LEDs-by-glowingkitty/GlowHub/GlowHubPCB/GlowHubPCBfiles.png

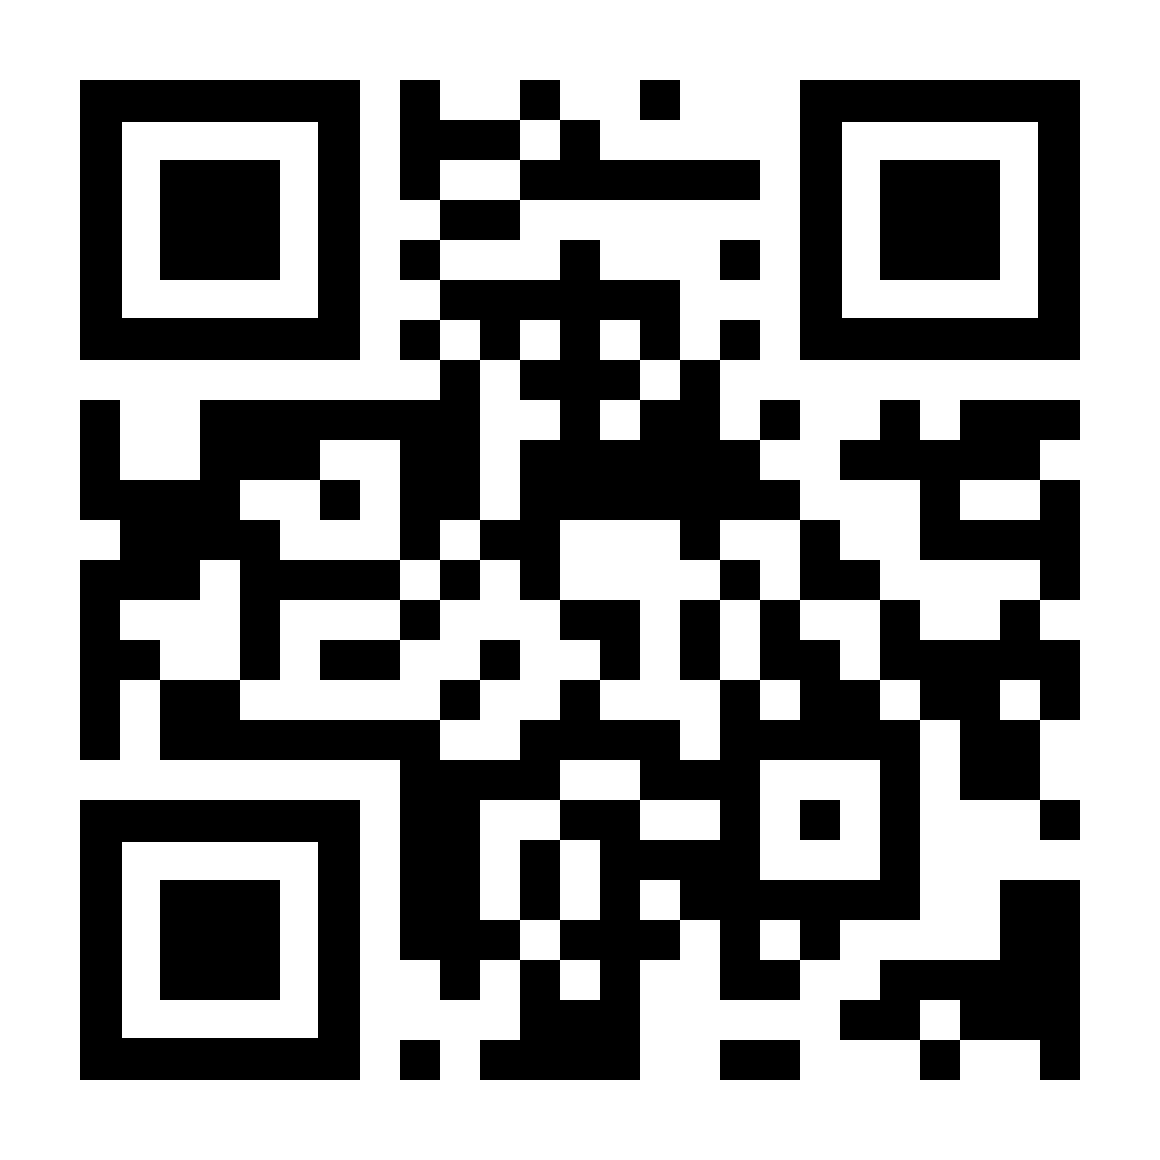
GlowHubPCB/GlowHubPCBfiles.png
