LEDs-by-glowingkitty/GlowHub/readme/wires_esp32_to_wago.jpg

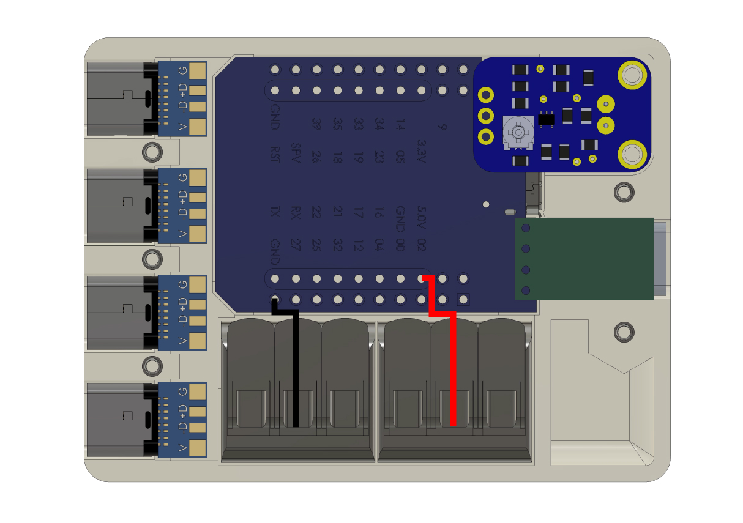
readme/wires_esp32_to_wago.jpg
