LEDs-by-glowingkitty/GlowHub/readme/build_2_add_electronics.gif

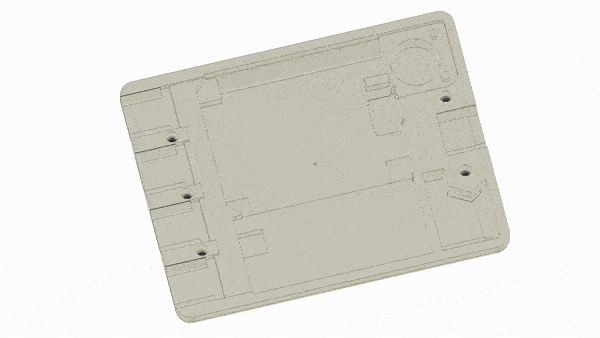
readme/build_2_add_electronics.gif
