LEDs-by-glowingkitty/GlowHub/readme/build_3_close_case.gif

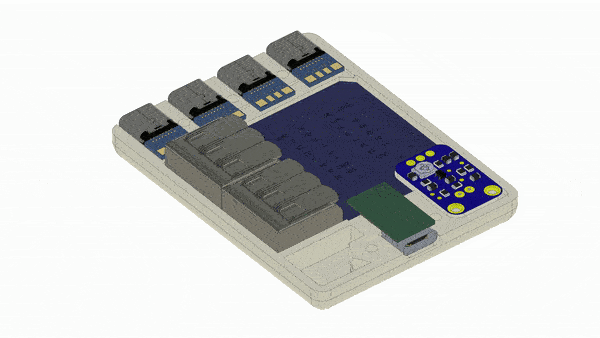
readme/build_3_close_case.gif
